igorwolfs/acoustic-piezodriver-hw/simulations/schematics/NFET_ENABLE.asc

D1: diode; 1N914
M1: pmos; AO3423
R1: res; 20k
R2: res; 30k
V1: voltage; 5
Named nets: 0
.tran 0 0.1m 0 1e-9
