igorwolfs/acoustic-piezodriver-hw/simulations/schematics/boost_20V.asc

C2: cap; 1nF
C3: cap; 100nF
C5: cap; 100p
C_in: cap; 24.7µF
C_out: cap; 88µF
D1: diode; 1N4148
L1: ind; 10µH; Rser=0.03
L2: ind; 10µH; Rser=0.03
L3: ind; 1nF; Rser=10
M2: nmos; IRLML6344
R1: res; 39k
R2: res; 30k
R3: res; 39k
R4: res; 0.02
R5: res; 0.01
R6: res; 25
R7: res; 1k
U1: LM3478_TRANS
V1: voltage; 20
Named nets: 0
.tran 0 100e-3 0 1e-6
DIODE: SS24 (Vf = 0.5) -> Should be SS14 (Vf=
FET: Choose between AO3400A or SI7454DP
Adding 100 pF between feedback and ground to reducec noise
Adding 1 nF between feedback and ground to reduce noise
Output current: 0.5 amps RMS, with 1 amp peak
COUPLING CAPACITORS
- Put 2 capacitors in parallel
- Made them slightly different to check effect
