igorwolfs/acoustic-piezodriver-hw/simulations/schematics/BVD_V1.asc

C1: cap; 2.6325e-10
C2: cap; 1.3e-9
L1: ind; 3.33e-5
R1: res; 2
V1: voltage; ""; AC 1
Named nets: 0, input, output
.ac oct 1000 1e3 10e6
