igorwolfs/acoustic-piezodriver-hw/simulations/schematics/full_bridge_driver.asc

C1: cap; 2.6325e-10
C2: cap; 1.3e-9
C3: cap; {Cboot}
C4: cap; {Cboot}
C5: cap; 1nF
C6: cap; 1nF
C7: cap; 1�F
C8: cap; 1�F
L1: ind; 3.33e-5
L2: ind; 5e-9; Rser=5
L3: ind; 5e-9; Rser=5
R1: res; 2
R2: res; {Rin_H}
R3: res; {Rin_L}
R4: res; {Rout_L}
R5: res; {Rout_H}
R7: res; {Rin_H}
R8: res; {Rout_L}
R9: res; {Rin_L}
R10: res; {Rout_H}
U1: UCC27282
U2: UCC27282
U3: Si7454DP
U8: Si7454DP
U9: Si7454DP
U10: Si7454DP
V1: voltage; 3.3
V2: voltage; 40
V3: voltage; 12
V4: voltage; PWL REPEAT FOREVER ((0 0) ({dt} 0) ({{dt}+10n} 3.3) ({{t}-10n} 3.3) ({t} 0) ({2*{t}-10n} 0) ({2*{t}} 0)) ENDREPEAT
V5: voltage; PWL REPEAT FOREVER ((0  0)   ({{t}+{dt}}  0) ({{t}+10n+{dt}} 3.3) ({2*{t}-10n} 3.3) ({2*{t}} 0)) ENDREPEAT
V6: voltage; 25
V7: voltage; PWL REPEAT FOREVER ((0 0) ({dt} 0) ({{dt}+10n} 3.3) ({{t}-10n} 3.3) ({t} 0) ({2*{t}-10n} 0) ({2*{t}} 0)) ENDREPEAT
V9: voltage; 3.3
V10: voltage; 12
V11: voltage; PWL REPEAT FOREVER ((0  0)   ({{t}+{dt}}  0) ({{t}+10n+{dt}} 3.3) ({2*{t}-10n} 3.3) ({2*{t}} 0)) ENDREPEAT
Named nets: 0
.param Rout_H=10 Rout_L=10 Rin_H=0.1 Rin_L=0.1 Cboot=230e-9 t=300e-9 dt=20e-9
Simulation
-> 1/(1.7e6) / 2 = 300 ns PWM signal
-> 0->300 ns high, 300->600ns
Adding input resistors and true differential PWM
-> Needed in case of a voltage drop in MCU
-> common mode noise is filtered out from the driving circuit
Shoot-through circuitry
-> Try to add dead-time / model parasitics which should prevent shoot-through
OFFSET FROM 300 ns
- There is a pretty significant conduction delay / rise time at these high frequencies
- That is the main reason why the actual FET switching has a 50-100 ns delay
- On top of that the spice-model used is worse than the one we are actually using
.tran 0 30e-6 0 0.1e-9
- 1 nF Filter capacitor at EN
- 1 uF decoupling capacitor at Vcc
.meas TRAN PERIODIC_CURRENT_INTEGRAL INTEG I(C2)+I(R1) FROM 10.44u TO 10.74u
.meas TRAN PEAK_CURRENT_INTEGRAL INTEG I(C2)+I(R1) FROM 10.524u TO 10.536u
.meas TRAN AVERAGE_CURRENT PERIODIC_CURRENT_INTEGRAL / {t*2}
.meas TRAN RMS_CURRENT RMS I(C2)+I(R1) FROM 10.0u TO 10.6u
