igorwolfs/acoustic-piezodriver-hw/simulations/schematics/lm3478_test.asc

C2: cap; 0.01µF
C3: cap; 22nF
C_in: cap; 100µF
C_out: cap; 100µF
D1: diode
L1: ind; 10µH
R1: res; 40k
R2: res; 60k
R3: res; 20k
R4: res; 0.025
R5: res; 4.7k
R6: res; 20
U2: LM3478_TRANS
U3: irf7807
V1: voltage; 3.3
Named nets: 0
.tran 0 10e-3 0 100e-9
