igorwolfs/acoustic-piezodriver-hw/simulations/schematics/sepic_10V.asc

C2: cap; 1nF
C3: cap; 220n
C4: cap; 33p
C5: cap; 100pF
C6: cap; 4.7µF; Rser=2.3e-3 Lser=3e-9
C_in: cap; 24.7
C_out: cap; 88µF
D1: schottky; SS24
L1: ind; 100µH; Rser=0.3
L2: ind; 100µH; Rser=0.3
L3: ind; 1nF; Rser=10
M2: nmos; IRLML6344
R1: res; 39k
R2: res; 4.7e3
R3: res; 2.7k
R4: res; 0.05
R5: res; 2.4k
R6: res; 15
R7: res; 680
U1: LM3478_TRANS
V1: voltage; 20
Named nets: 0
.tran 0 100e-3 0 1e-6
DIODE: SS24 (Vf = 0.5) -> Should be SS14 (Vf=
FET: Choose between AO3400A or SI7454DP
Adding 100 pF between feedback and ground to reducec noise
Adding 1 nF between feedback and ground to reduce noise
Output current: 0.5 amps RMS, with 1 amp peak
COUPLING CAPACITORS
- Put 2 capacitors in parallel
- Made them slightly different to check effect
